AidanHockey5/STM32_VGM_Player_YM2612_SN76489/src/logo.h

#define logo_width 128
#define logo_height 64
#include <Arduino.h>
const static uint8_t logo[]{
  0x3F, 0x80, 0x1F, 0xF8, 0x3F, 0xF0, 0xFF, 0x01, 0x3C, 0x00, 0x00, 0x00, 
  0x00, 0x00, 0x00, 0x00, 0x3F, 0x80, 0x1F, 0xFC, 0x3F, 0xFC, 0xFF, 0x01, 
  0x7E, 0x00, 0x00, 0x00, 0x00, 0x00, 0x00, 0x00, 0x3F, 0x80, 0x1F, 0xFE, 
  0x3F, 0xFE, 0xFF, 0x01, 0x7E, 0x00, 0x73, 0x18, 0x03, 0x80, 0x10, 0x0C, 
  0x7F, 0xC0, 0x1F, 0x1F, 0x00, 0x3E, 0x00, 0x00, 0xFE, 0x80, 0x8C, 0x24, 
  0x02, 0x00, 0x09, 0x12, 0x7F, 0xC0, 0x1F, 0x0F, 0x00, 0x1F, 0x00, 0x00, 
  0xFF, 0x00, 0x8C, 0x20, 0x02, 0x00, 0x09, 0x10, 0x7F, 0xC0, 0x9F, 0x0F, 
  0x00, 0x0F, 0x00, 0x00, 0xFF, 0x00, 0x8A, 0x10, 0x02, 0x07, 0x09, 0x0C, 
  0xEF, 0xE0, 0x9E, 0x07, 0x00, 0x0F, 0x00, 0x80, 0xE7, 0x01, 0x89, 0x08, 
  0x02, 0x00, 0x06, 0x10, 0xEF, 0xE0, 0x9E, 0x07, 0x00, 0x0F, 0x00, 0x80, 
  0xE7, 0x81, 0x88, 0x04, 0x02, 0x00, 0x06, 0x12, 0xEF, 0xE0, 0x9E, 0xFF, 
  0xBF, 0x0F, 0xFF, 0x81, 0xC7, 0x83, 0x77, 0x3C, 0x02, 0x00, 0x46, 0x0C, 
  0xCF, 0x71, 0x9E, 0xFF, 0xBF, 0x0F, 0xFF, 0xC1, 0xC3, 0x03, 0x00, 0x00, 
  0x00, 0x00, 0x00, 0x00, 0xCF, 0x71, 0x9E, 0xFF, 0xBF, 0x0F, 0xFF, 0xC1, 
  0xC3, 0x03, 0x00, 0x00, 0x00, 0x00, 0x00, 0x00, 0xCF, 0x71, 0x9E, 0x07, 
  0x00, 0x0F, 0xE0, 0xE1, 0x81, 0x07, 0x00, 0x00, 0x00, 0x00, 0x00, 0x00, 
  0x8F, 0x3B, 0x9E, 0x07, 0x00, 0x0F, 0xE0, 0xE1, 0xFF, 0x07, 0x00, 0x00, 
  0x00, 0x00, 0x00, 0x00, 0x8F, 0x3B, 0x9E, 0x0F, 0x00, 0x0F, 0xE0, 0xE1, 
  0xFF, 0x0F, 0x00, 0x00, 0x00, 0x00, 0x00, 0x00, 0x8F, 0x3B, 0x1E, 0x0F, 
  0x00, 0x1F, 0xE0, 0xF1, 0x00, 0x0F, 0x00, 0x00, 0x00, 0x00, 0x00, 0x00, 
  0x8F, 0x1F, 0x1E, 0x1F, 0x00, 0x3E, 0xE0, 0xF1, 0x00, 0x1F, 0x00, 0x00, 
  0x00, 0x00, 0x00, 0x00, 0x0F, 0x1F, 0x1E, 0xFE, 0x3F, 0xFE, 0xFF, 0x79, 
  0x00, 0x1E, 0x00, 0x00, 0x00, 0x00, 0x00, 0x00, 0x0F, 0x1F, 0x1E, 0xFC, 
  0x3F, 0xFC, 0xFF, 0x79, 0x00, 0x1E, 0x00, 0x00, 0x00, 0x00, 0x00, 0x00, 
  0x0F, 0x1F, 0x1E, 0xF8, 0x3F, 0xF0, 0xFF, 0x7D, 0x00, 0x3C, 0x00, 0x00, 
  0x00, 0x00, 0x00, 0x00, 0x00, 0x00, 0x00, 0x00, 0x00, 0x00, 0x00, 0x00, 
  0x00, 0x00, 0x00, 0x00, 0x00, 0x00, 0x00, 0x00, 0xFF, 0x1F, 0x78, 0x00, 
  0x00, 0x0F, 0x80, 0xFF, 0xDF, 0xFF, 0x3F, 0xFC, 0x9F, 0xFF, 0x0F, 0x00, 
  0xFF, 0x7F, 0x78, 0x00, 0x80, 0x1F, 0xC0, 0xFF, 0xDF, 0xFF, 0x3F, 0xFE, 
  0x9F, 0xFF, 0x3F, 0x00, 0xFF, 0xFF, 0x78, 0x00, 0x80, 0x1F, 0xE0, 0xFF, 
  0xDF, 0xFF, 0x3F, 0xFF, 0x9F, 0xFF, 0x7F, 0x00, 0x0F, 0xF8, 0x79, 0x00, 
  0x80, 0x3F, 0xE0, 0x03, 0x00, 0xF0, 0x80, 0x0F, 0x80, 0x07, 0x7C, 0x00, 
  0x0F, 0xE0, 0x79, 0x00, 0xC0, 0x3F, 0xE0, 0x01, 0x00, 0xF0, 0x80, 0x07, 
  0x80, 0x07, 0x7C, 0x00, 0x0F, 0xE0, 0x79, 0x00, 0xC0, 0x3F, 0xF0, 0x01, 
  0x00, 0xF0, 0xC0, 0x07, 0x80, 0x07, 0x78, 0x00, 0x0F, 0xE0, 0x79, 0x00, 
  0xE0, 0x79, 0xE0, 0x01, 0x00, 0xF0, 0xC0, 0x03, 0x80, 0x07, 0x7C, 0x00, 
  0x0F, 0xF0, 0x78, 0x00, 0xE0, 0x79, 0xE0, 0x07, 0x00, 0xF0, 0xC0, 0x03, 
  0x80, 0x07, 0x7C, 0x00, 0xFF, 0xFF, 0x78, 0x00, 0xE0, 0xF1, 0xE0, 0xFF, 
  0x0F, 0xF0, 0xC0, 0xFF, 0x9F, 0xFF, 0x7F, 0x00, 0xFF, 0x3F, 0x78, 0x00, 
  0xF0, 0xF0, 0xC0, 0xFF, 0x1F, 0xF0, 0xC0, 0xFF, 0x9F, 0xFF, 0x3F, 0x00, 
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
