AidanHockey5/STM32_VGM_Player_YM2612_SN76489/tools/MegaFlasher_MB/FLASH_FIRMWARE/dev_table.c

/*
  stm32flash - Open Source ST STM32 flash program for *nix
  Copyright (C) 2010 Geoffrey McRae <geoff@spacevs.com>
  Copyright (C) 2014-2015 Antonio Borneo <borneo.antonio@gmail.com>

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
  You should have received a copy of the GNU General Public License
  along with this program; if not, write to the Free Software
  Foundation, Inc., 51 Franklin Street, Fifth Floor, Boston, MA  02110-1301, USA.
*/

#include "stm32.h"

#define SZ_128	0x00000080
#define SZ_256	0x00000100
#define SZ_1K	0x00000400
#define SZ_2K	0x00000800
#define SZ_16K	0x00004000
#define SZ_32K	0x00008000
#define SZ_64K	0x00010000
#define SZ_128K	0x00020000
#define SZ_256K	0x00040000

/*
 * Page-size for page-by-page flash erase.
 * Arrays are zero terminated; last non-zero value is automatically repeated
 */

/* fixed size pages */
static uint32_t p_128[] = { SZ_128, 0 };
static uint32_t p_256[] = { SZ_256, 0 };
static uint32_t p_1k[]  = { SZ_1K,  0 };
static uint32_t p_2k[]  = { SZ_2K,  0 };
/* F2 and F4 page size */
static uint32_t f2f4[]  = { SZ_16K, SZ_16K, SZ_16K, SZ_16K, SZ_64K, SZ_128K, 0 };
/* F4 dual bank page size */
static uint32_t f4db[]  = {
	SZ_16K, SZ_16K, SZ_16K, SZ_16K, SZ_64K, SZ_128K, SZ_128K, SZ_128K,
	SZ_16K, SZ_16K, SZ_16K, SZ_16K, SZ_64K, SZ_128K, 0
};
/* F7 page size */
static uint32_t f7[]    = { SZ_32K, SZ_32K, SZ_32K, SZ_32K, SZ_128K, SZ_256K, 0 };

/*
 * Device table, corresponds to the "Bootloader device-dependant parameters"
 * table in ST document AN2606.
 * Note that the option bytes upper range is inclusive!
 */
const stm32_dev_t devices[] = {
	/* ID   "name"                              SRAM-address-range      FLASH-address-range    PPS  PSize   Option-byte-addr-range  System-mem-addr-range   Flags */
	/* F0 */
	{0x440, "STM32F030x8/F05xxx"              , 0x20000800, 0x20002000, 0x08000000, 0x08010000,  4, p_1k  , 0x1FFFF800, 0x1FFFF80F, 0x1FFFEC00, 0x1FFFF800, 0},
	{0x442, "STM32F030xC/F09xxx"              , 0x20001800, 0x20008000, 0x08000000, 0x08040000,  2, p_2k  , 0x1FFFF800, 0x1FFFF80F, 0x1FFFC800, 0x1FFFF800, F_OBLL},
	{0x444, "STM32F03xx4/6"                   , 0x20000800, 0x20001000, 0x08000000, 0x08008000,  4, p_1k  , 0x1FFFF800, 0x1FFFF80F, 0x1FFFEC00, 0x1FFFF800, 0},
	{0x445, "STM32F04xxx/F070x6"              , 0x20001800, 0x20001800, 0x08000000, 0x08008000,  4, p_1k  , 0x1FFFF800, 0x1FFFF80F, 0x1FFFC400, 0x1FFFF800, 0},
	{0x448, "STM32F070xB/F071xx/F72xx"        , 0x20001800, 0x20004000, 0x08000000, 0x08020000,  2, p_2k  , 0x1FFFF800, 0x1FFFF80F, 0x1FFFC800, 0x1FFFF800, 0},
	/* F1 */
	{0x412, "STM32F10xxx Low-density"         , 0x20000200, 0x20002800, 0x08000000, 0x08008000,  4, p_1k  , 0x1FFFF800, 0x1FFFF80F, 0x1FFFF000, 0x1FFFF800, 0},
	{0x410, "STM32F10xxx Medium-density"      , 0x20000200, 0x20005000, 0x08000000, 0x08020000,  4, p_1k  , 0x1FFFF800, 0x1FFFF80F, 0x1FFFF000, 0x1FFFF800, 0},
	{0x414, "STM32F10xxx High-density"        , 0x20000200, 0x20010000, 0x08000000, 0x08080000,  2, p_2k  , 0x1FFFF800, 0x1FFFF80F, 0x1FFFF000, 0x1FFFF800, 0},
	{0x420, "STM32F10xxx Medium-density VL"   , 0x20000200, 0x20002000, 0x08000000, 0x08020000,  4, p_1k  , 0x1FFFF800, 0x1FFFF80F, 0x1FFFF000, 0x1FFFF800, 0},
	{0x428, "STM32F10xxx High-density VL"     , 0x20000200, 0x20008000, 0x08000000, 0x08080000,  2, p_2k  , 0x1FFFF800, 0x1FFFF80F, 0x1FFFF000, 0x1FFFF800, 0},
	{0x418, "STM32F105xx/F107xx"              , 0x20001000, 0x20010000, 0x08000000, 0x08040000,  2, p_2k  , 0x1FFFF800, 0x1FFFF80F, 0x1FFFB000, 0x1FFFF800, 0},
	{0x430, "STM32F10xxx XL-density"          , 0x20000800, 0x20018000, 0x08000000, 0x08100000,  2, p_2k  , 0x1FFFF800, 0x1FFFF80F, 0x1FFFE000, 0x1FFFF800, 0},
	/* F2 */
	{0x411, "STM32F2xxxx"                     , 0x20002000, 0x20020000, 0x08000000, 0x08100000,  1, f2f4  , 0x1FFFC000, 0x1FFFC00F, 0x1FFF0000, 0x1FFF7800, 0},
	/* F3 */
	{0x432, "STM32F373xx/F378xx"              , 0x20001400, 0x20008000, 0x08000000, 0x08040000,  2, p_2k  , 0x1FFFF800, 0x1FFFF80F, 0x1FFFD800, 0x1FFFF800, 0},
	{0x422, "STM32F302xB(C)/F303xB(C)/F358xx" , 0x20001400, 0x2000A000, 0x08000000, 0x08040000,  2, p_2k  , 0x1FFFF800, 0x1FFFF80F, 0x1FFFD800, 0x1FFFF800, 0},
	{0x439, "STM32F301xx/F302x4(6/8)/F318xx"  , 0x20001800, 0x20004000, 0x08000000, 0x08010000,  2, p_2k  , 0x1FFFF800, 0x1FFFF80F, 0x1FFFD800, 0x1FFFF800, 0},
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
	{0x9b0, "STM32W-256K"                     , 0x20000200, 0x20004000, 0x08000000, 0x08040000,  4, p_2k  , 0x08040800, 0x0804080F, 0x08040000, 0x08040800, 0},
	{0x0}
};
