AidanHockey5/STM32_VGM_Player_YM2612_SN76489/tools/MegaFlasher_MB/FLASH_FIRMWARE/init.c

/*
  stm32flash - Open Source ST STM32 flash program for *nix
  Copyright (C) 2010 Geoffrey McRae <geoff@spacevs.com>
  Copyright (C) 2013 Antonio Borneo <borneo.antonio@gmail.com>

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
  You should have received a copy of the GNU General Public License
  along with this program; if not, write to the Free Software
  Foundation, Inc., 51 Franklin Street, Fifth Floor, Boston, MA  02110-1301, USA.
*/


#include <ctype.h>
#include <errno.h>
#include <fcntl.h>
#include <stdint.h>
#include <stdio.h>
#include <stdlib.h>
#include <string.h>
#include <unistd.h>
#include <sys/stat.h>
#include "init.h"
#include "serial.h"
#include "stm32.h"
#include "port.h"

struct gpio_list {
	struct gpio_list *next;
	int gpio;
	int input; /* 1 if direction of gpio should be changed back to input. */
	int exported; /* 0 if gpio should be unexported. */
};

static int write_to(const char *filename, const char *value)
{
	int fd, ret;

	fd = open(filename, O_WRONLY);
	if (fd < 0) {
		fprintf(stderr, "Cannot open file \"%s\"\n", filename);
		return 0;
	}
	ret = write(fd, value, strlen(value));
	if (ret < 0) {
		fprintf(stderr, "Error writing in file \"%s\"\n", filename);
		close(fd);
		return 0;
	}
	close(fd);
	return 1;
}

#if !defined(__linux__)
static int drive_gpio(int n, int level, struct gpio_list **gpio_to_release)
{
	fprintf(stderr, "GPIO control only available in Linux\n");
	return 0;
}
#else
static int read_from(const char *filename, char *buf, size_t len)
{
	int fd, ret;
	ssize_t n = 0;

	fd = open(filename, O_RDONLY);
	if (fd < 0) {
		fprintf(stderr, "Cannot open file \"%s\"\n", filename);
		return 0;
	}

	do {
		ret = read(fd, buf + n, len - n);
		if (ret < 0) {
			if (errno == EINTR || errno == EAGAIN || errno == EWOULDBLOCK)
				continue; /* try again */
			fprintf(stderr, "Error reading in file \"%s\"\n", filename);
			close(fd);
			return 0;
		}
		n += ret;
	} while (n < len && ret);

	close(fd);
	return n;
}

static int drive_gpio(int n, int level, struct gpio_list **gpio_to_release)
{
	char num[16]; /* sized to carry MAX_INT */
	char file[48]; /* sized to carry longest filename */
	char dir;
	struct stat buf;
	struct gpio_list *new;
	int ret;
	int exported = 1;
	int input = 0;

	sprintf(file, "/sys/class/gpio/gpio%d/value", n);
	ret = stat(file, &buf);
	if (ret) {
		/* file miss, GPIO not exported yet */
		sprintf(num, "%d", n);
		ret = write_to("/sys/class/gpio/export", num);
		if (!ret)
			return 0;
		ret = stat(file, &buf);
		if (ret) {
			fprintf(stderr, "GPIO %d not available\n", n);
			return 0;
		}
		exported = 0;
	}

	sprintf(file, "/sys/class/gpio/gpio%d/direction", n);
	ret = stat(file, &buf);
	if (!ret)
		if (read_from(file, &dir, sizeof(dir)))
			if (dir == 'i')
				input = 1;

	if (exported == 0 || input == 1) {
		new = (struct gpio_list *)malloc(sizeof(struct gpio_list));
		if (new == NULL) {
			fprintf(stderr, "Out of memory\n");
			return 0;
		}
		new->gpio = n;
		new->exported = exported;
		new->input = input;
		new->next = *gpio_to_release;
		*gpio_to_release = new;
	}

	return write_to(file, level ? "high" : "low");
}
#endif

static int release_gpio(int n, int input, int exported)
{
	char num[16]; /* sized to carry MAX_INT */
	char file[48]; /* sized to carry longest filename */

	sprintf(num, "%d", n);
	if (input) {
		sprintf(file, "/sys/class/gpio/gpio%d/direction", n);
		write_to(file, "in");
	}
	if (!exported)
		write_to("/sys/class/gpio/unexport", num);

	return 1;
}

static int gpio_sequence(struct port_interface *port, const char *s, size_t l)
{
	struct gpio_list *gpio_to_release = NULL, *to_free;
	int ret, level, gpio;

	ret = 1;
	while (ret == 1 && *s && l > 0) {
		if (*s == '-') {
			level = 0;
			s++;
			l--;
		} else
			level = 1;

		if (isdigit(*s)) {
			gpio = atoi(s);
			while (isdigit(*s)) {
				s++;
				l--;
			}
		} else if (!strncmp(s, "rts", 3)) {
			gpio = -GPIO_RTS;
			s += 3;
			l -= 3;
		} else if (!strncmp(s, "dtr", 3)) {
			gpio = -GPIO_DTR;
			s += 3;
			l -= 3;
		} else if (!strncmp(s, "brk", 3)) {
			gpio = -GPIO_BRK;
			s += 3;
			l -= 3;
		} else {
			fprintf(stderr, "Character \'%c\' is not a digit\n", *s);
			ret = 0;
			break;
		}

		if (*s && (l > 0)) {
			if (*s == ',') {
				s++;
				l--;
			} else {
				fprintf(stderr, "Character \'%c\' is not a separator\n", *s);
				ret = 0;
				break;
			}
		}
		if (gpio < 0)
			ret = (port->gpio(port, -gpio, level) == PORT_ERR_OK);
		else
			ret = drive_gpio(gpio, level, &gpio_to_release);
		usleep(100000);
	}

	while (gpio_to_release) {
		release_gpio(gpio_to_release->gpio, gpio_to_release->input, gpio_to_release->exported);
		to_free = gpio_to_release;
		gpio_to_release = gpio_to_release->next;
		free(to_free);
	}
	usleep(500000);
	return ret;
}

static int gpio_bl_entry(struct port_interface *port, const char *seq)
{
	char *s;

	if (seq == NULL || seq[0] == ':')
		return 1;

	s = strchr(seq, ':');
	if (s == NULL)
		return gpio_sequence(port, seq, strlen(seq));

	return gpio_sequence(port, seq, s - seq);
}

static int gpio_bl_exit(struct port_interface *port, const char *seq)
{
	char *s;

	if (seq == NULL)
		return 1;

	s = strchr(seq, ':');
	if (s == NULL || s[1] == '\0')
		return 1;

	return gpio_sequence(port, s + 1, strlen(s + 1));
}

int init_bl_entry(struct port_interface *port, const char *seq)
{
	if (seq)
		return gpio_bl_entry(port, seq);

	return 1;
}

int init_bl_exit(stm32_t *stm, struct port_interface *port, const char *seq)
{
	if (seq && strchr(seq, ':'))
		return gpio_bl_exit(port, seq);

	if (stm32_reset_device(stm) != STM32_ERR_OK)
		return 0;
	return 1;
}
